thebenheckshow/201-tbhs-oscilloscope-watch/case_design/STL/finger caps.stl

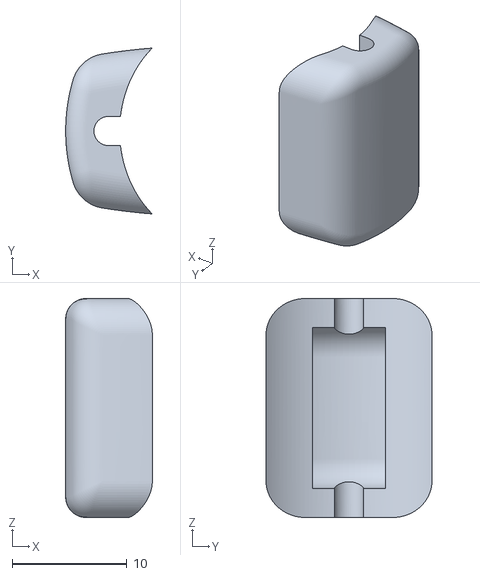
[picture p15: CAD file, 2015-09-09]
case_design/STL/finger caps.stl
7.54 x 14.4 x 19.1
